ShivinderK/Capstone_Project/HTML coding/HTML Coding.pdf

# IoT Based Garage Door

# Opener: HTML Coding for Web Page

### Dawinder Kaur

(C0765505)

### Group 4

## Content:

- Introduction of ESP32 Wifi Module
- Features of ESP32
- Pinout of ESP32
- Introduction to HTML Coding
- Versions of HTML
- Example of HTML Document
- What is HTML element
- HTML Page Structure
- Introduction of CSS3
- Features of CSS3
- CSS3 Example
- Advantages of CSS3
- References

## Introduction of ESP32 Wifi Module

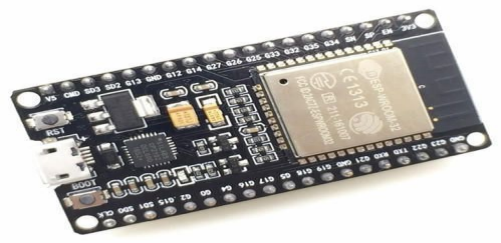
[picture p140: figure]

- ESP32 is a series of low-cost,
low-power system on a chip (https://en.wikipedia.org/wiki/System_on_a_chip)
microcontrollers (https://en.wikipedia.org/wiki/Microcontroller) with integrated Wi-Fi (https://en.wikipedia.org/wiki/Wi-Fi) and dual-mode Bluetooth. (https://en.wikipedia.org/wiki/Bluetooth)
- ESP32 is created and developed by Espressif Systems, a
Shanghai-based Chinese
company, and is manufactured by TSMC using their 40 nm
process.
- It is a successor to the ESP8266 microcontroller.

## Features of ESP32 Wifi module

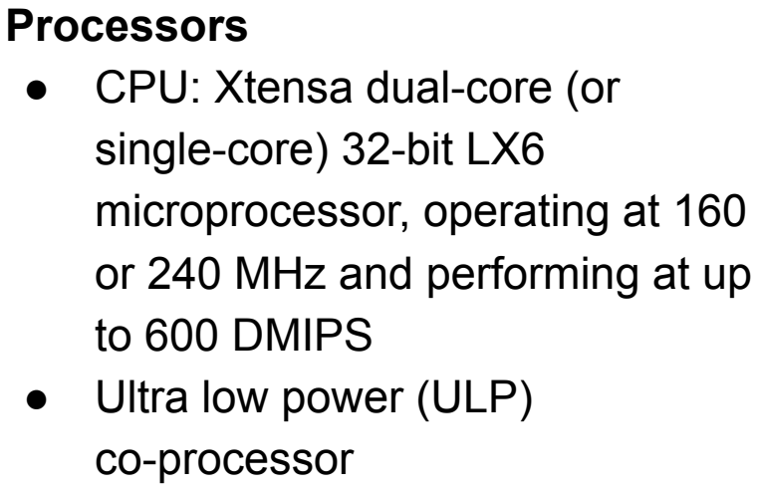
[picture p141: figure]
Processors ● CPU: Xtensa dual-core (or single-core) 32-bit LX6 microprocessor, operating at 160 or 240 MHz and performing at up to 600 DMIPS ● Ultra low power (ULP) co-processor

Peripheral interfaces
- 12-bit SAR ADC (https://en.wikipedia.org/wiki/Successive_approximation_ADC) up to 18
channels
- 2 × 8-bit DACs
- 10 × touch sensors
- 4 × SPI
- 2 × I²S and 2 x I²C interfaces
- 3 × UART
- MMC/eMMC host controller
- SDIO/SPI slave controller

## Features of ESP32 Wifi module

- Ethernet MAC interface with dedicated DMA and IEEE 1588 Precision Time Protocol support
- CAN bus 2.0
- Infrared remote controller (TX/RX, up to 8 channels)
- Motor PWM
- LED PWM (up to 16 channels)
- Hall effect sensor
- Ultra low power analog preamplifier

## Pin Diagram of ESP32 Wifi module

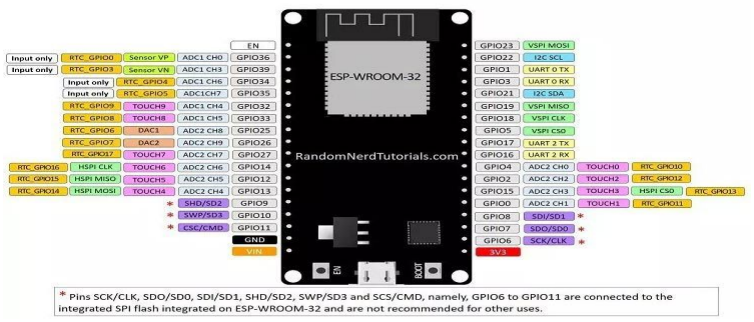
[picture p142: figure]

## Introduction to HTML Coding

HTML is the standard markup language for creating Web pages.

- HTML stands for Hyper Text Markup Language.
- It is a language that we use to create Web pages.
- It describes the structure of Web pages.
- It consists of a series of elements.
- HTML elements tell the browser how to display the content.
- HTML elements label pieces of content such as “this is a heading”, “this is a paragraph”, “this is a link”, etc.

## Introduction to HTML Coding

HTML Version:

- HTML 1.0
- HTML 2
- HTML 3.2
- HTML 4.01
- HTML 5

## Introduction to HTML Coding

HTML 5 is the latest version of HTML language. It was started to use in 2014 and it came up with lots of HTML tags support. It provided support for new form elements like input elements of different types, geolocations, support tags, etc.

The new tags that has been added are Email, password, audio tag, semantic tags and section tag.

## Introduction to HTML Coding

<!DOCTYPE html> | //this declares that this is an HTML5 document
<html> | //this is the root element of HTML page
<head> | //this contains meta information about HTML page
<title>Page Title</title> | //this element is shown in the browser’s title
</head>
<body> | //element defines the document’s body and is the

container for all visible contents like headings,

paragraphs, images, hyperlinks, etc

<h1>My First Heading</h1> | //defines a large heading
<p>My first paragraph.</p> | //defines a paragraph

</body>
</html>

## Introduction to HTML Coding

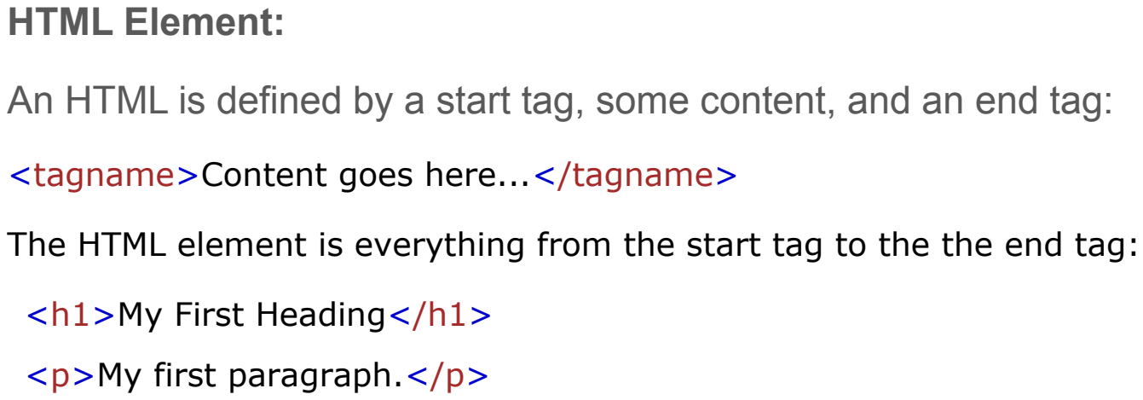
[picture p143: figure]
HTML Element:; <tagname>Content goes here...</tagname>; <h1>My First Heading</h1>; <p>My first paragraph.</p>

An HTML is defined by a start tag, some content, and an end tag:

The HTML element is everything from the start tag to the the end tag:

## Introduction to HTML Coding

Start Tag | Element Content | End Tag
<h1> | My First Heading | </h1>
<p> | My first paragraph | </p>
<br> | none | none

## Introduction to HTML Coding

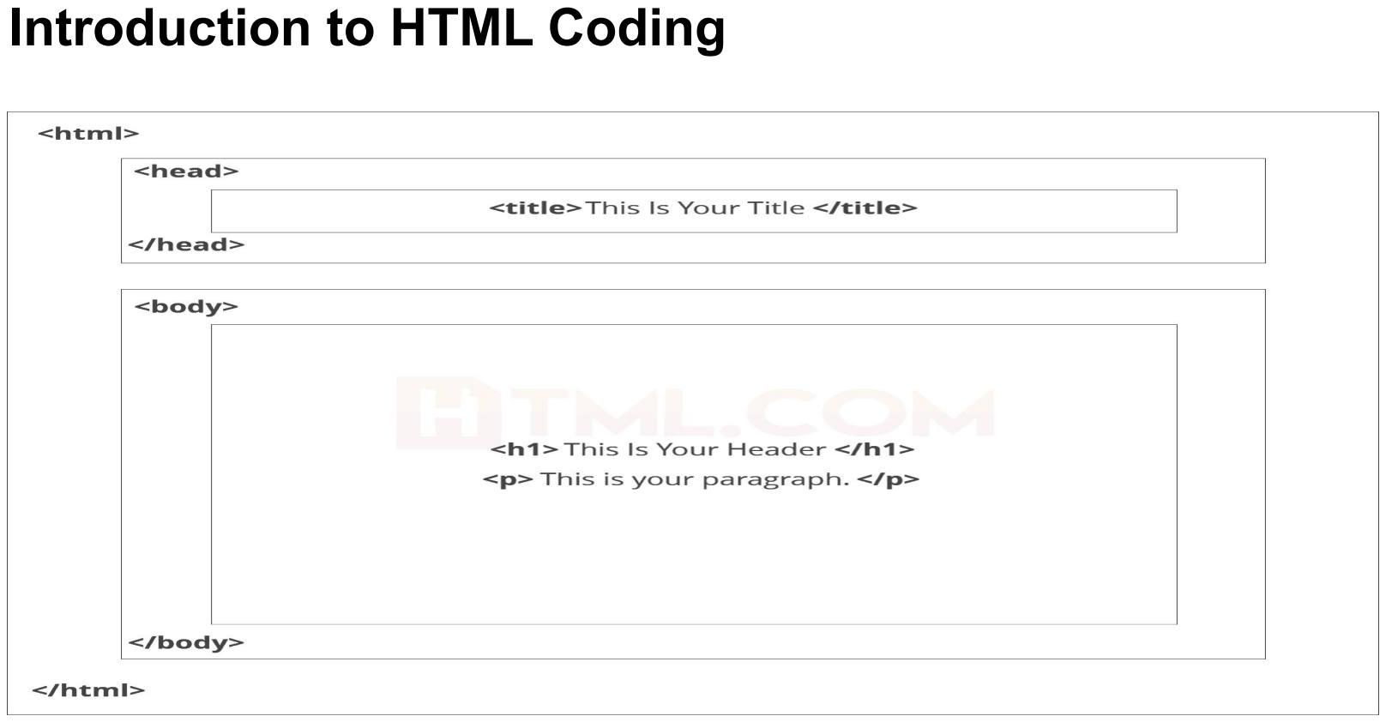
[picture p144: page 13]

## Introduction CSS3(Cascading Style Sheets):

Cascading Style Sheets (CSS) is a language that is used to illustrate the look, style, and format of a document written in any markup language.

In simple words, it is used to style and organize the layout of Web pages.

CSS3 is the latest version of an earlier CSS version, CSS2.

A significant change in CSS3 in comparison to CSS2 is the introduction of modules.

The benefit of this functionality is that it allows the specification to be finalized and accept faster, as segments are finalized and accepted in portions.

## Introduction CSS3(Cascading Style Sheets):

Some of the key modules of CSS3 are:

- Box model
- Image values and replaced content
- Text effects
- Selectors
- Backgrounds and borders
- Animations
- User interface (UI)
- Multiple column layouts
- 2D/3D transformations.

## Introduction CSS3(Cascading Style Sheets):

body | {
background-color: | lightblue;
}
h1 | { | //<h1> This is a heading
color: | white;
text-align: | center;
}
p | { | //<p> This is a paragraph
font-family: | verdana;
font-size: | 20px;
}

## Introduction CSS3(Cascading Style Sheets):

Advantages of CSS3

- CSS3 provides a consistent and precise positioning of navigable elements.
- It is easy to customize a web page as it can be done by merely altering a modular file.
- Graphics are easier in CSS3, thus making it easy to make the site appealing.
- It permits online videos to be seen without using third-party plug-ins.
- CSS3 is economical, time-saving, and most browsers support it.

## HTML Coding on Notepad:

HTML Programming on Notepad:

1. Open Notepad
2. Write HTML/CSS3 code
3. Save the file named as web.html (with .html extension so that it can run on browser).
4. Go to the location where u saved the file.
5. Click on file and choose open with chrome browser
6. Web page will appear on web browser.

## HTML Coding on Notepad:

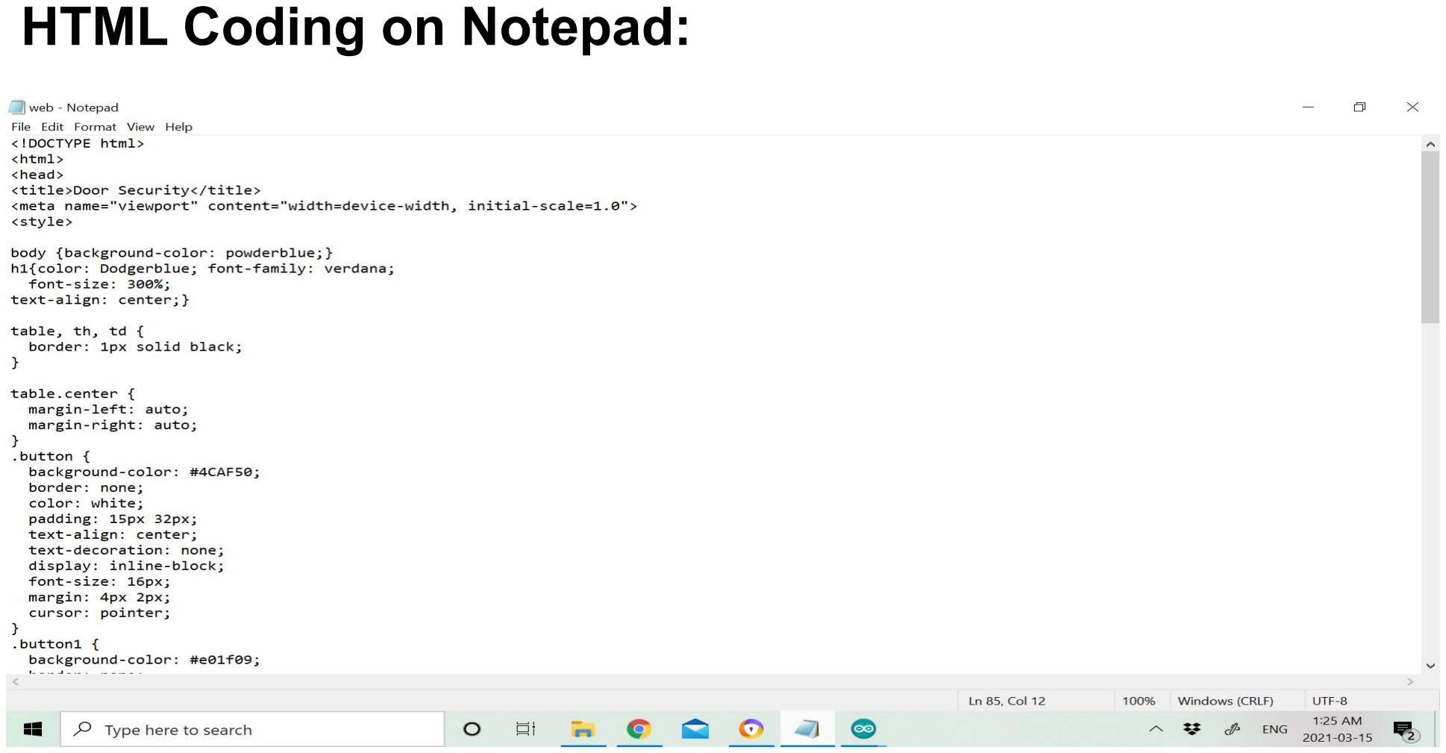
[picture p145: page 19]

## HTML Coding on Notepad:

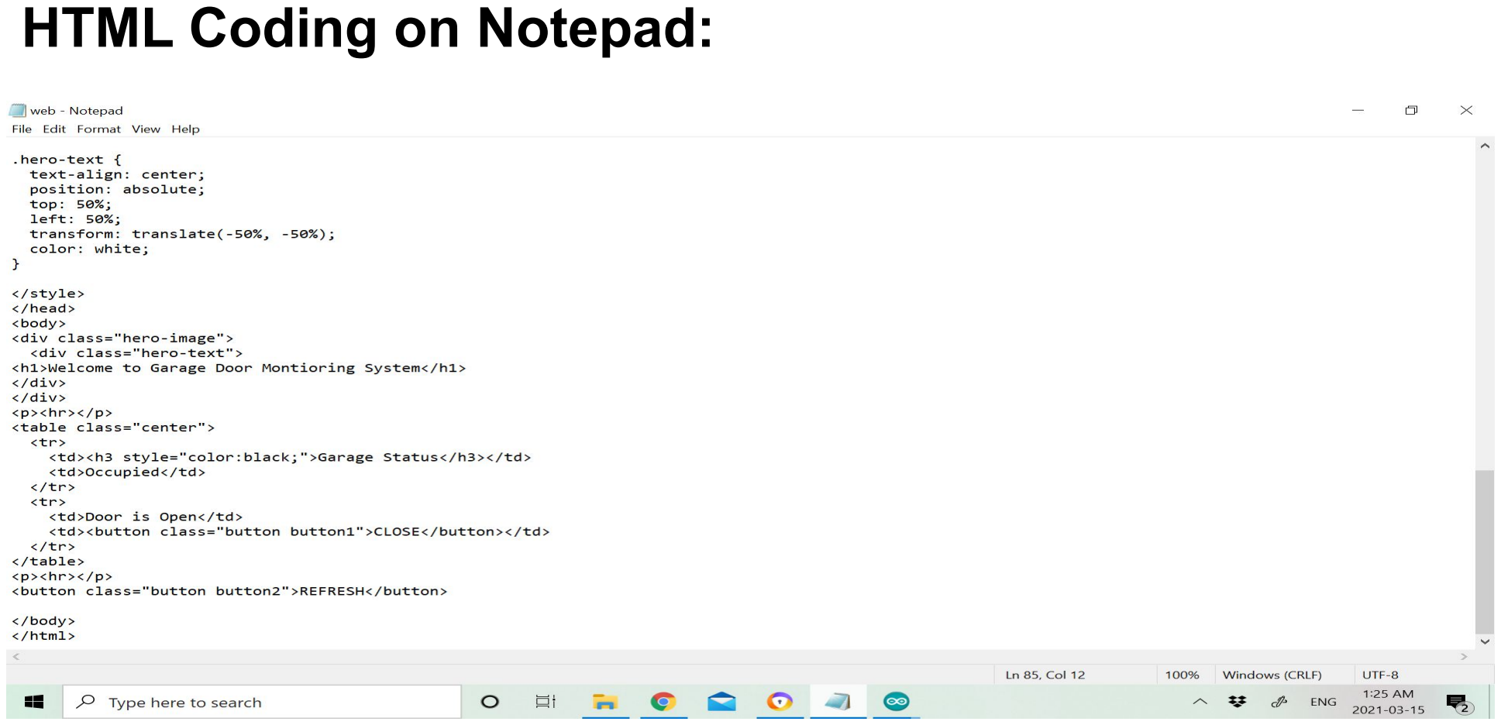
[picture p146: page 20]

## HTML Coding on Notepad: Output

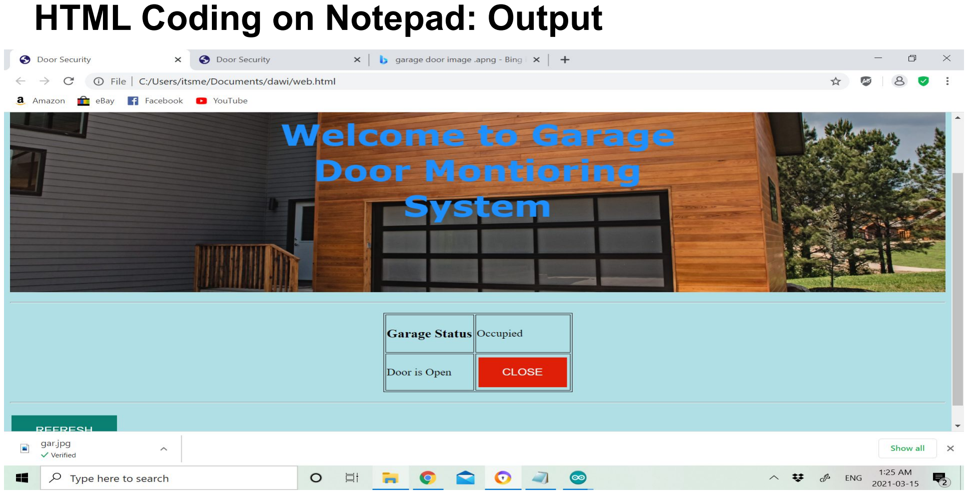
[picture p147: page 21]

## HTML coding on ESP32:

HTML coding on ESP32:

- Open arduino ide
- Write arduino ide code for esp32 wifi connectivity and in void loop{ } area add the html code using command “client.print {html code here}”
- Save the file
- Compile it and execute it by connecting ESP32 with system.
- Output will appear in serial monitor

## HTML coding on ESP32:

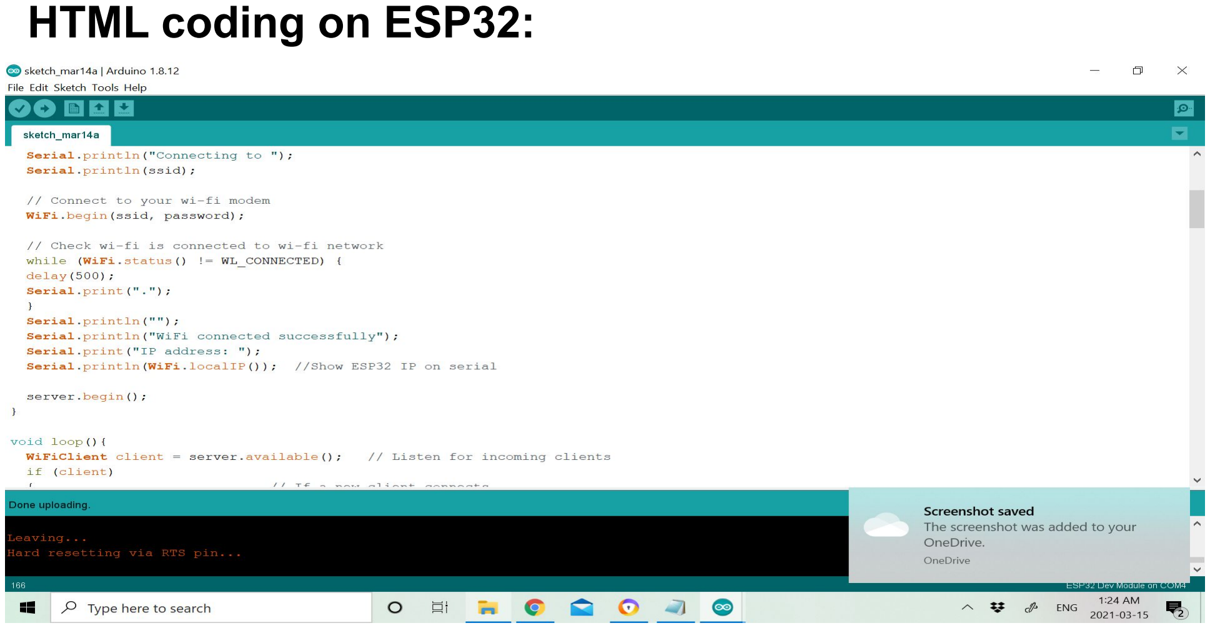
[picture p148: page 23]

## HTML coding on ESP32:

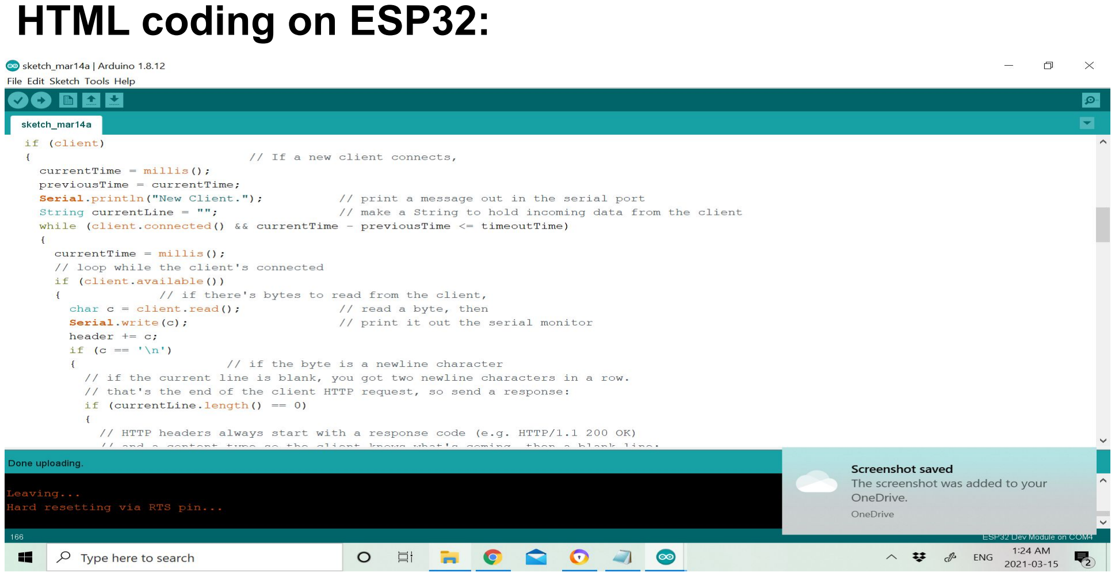
[picture p149: page 24]

## HTML coding on ESP32:

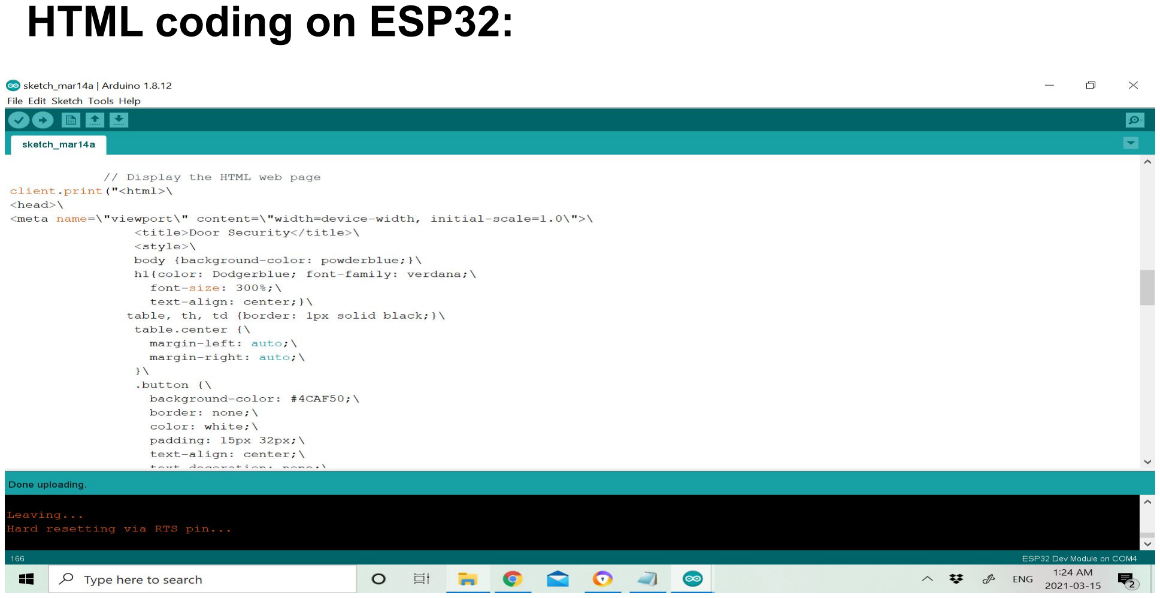
[picture p150: page 25]

## HTML coding on ESP32:

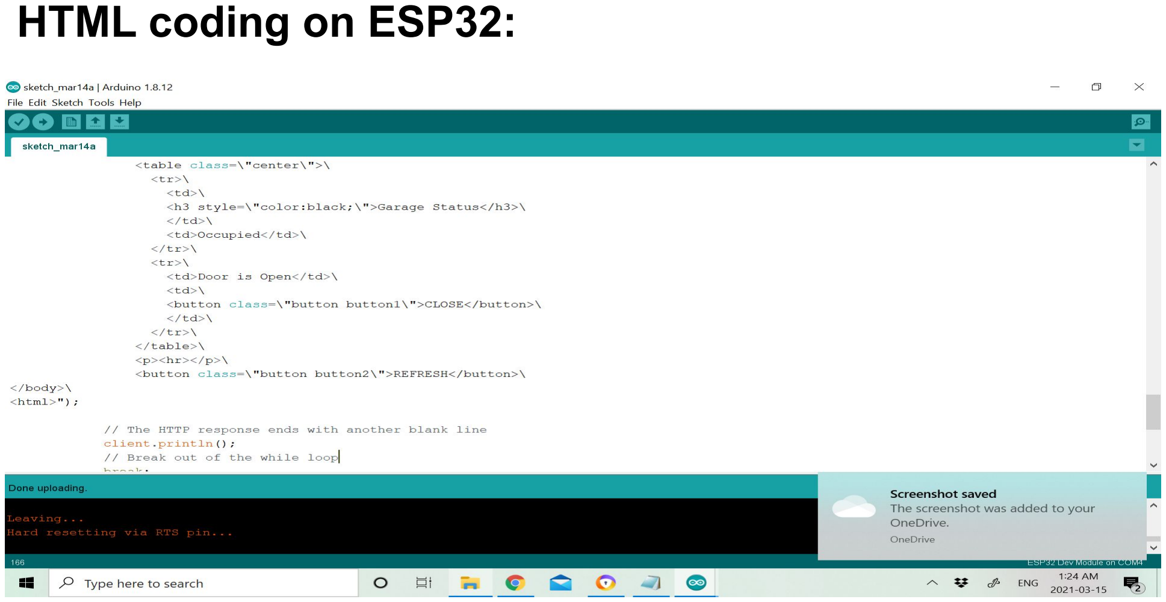
[picture p151: page 26]

## HTML coding on ESP32:

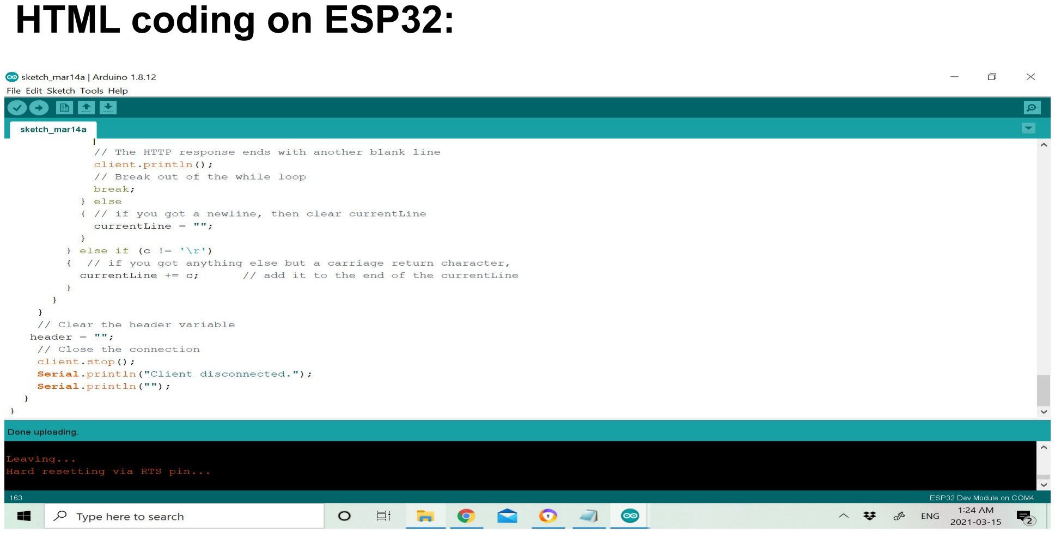
[picture p152: page 27]

## HTML coding on ESP32: Output

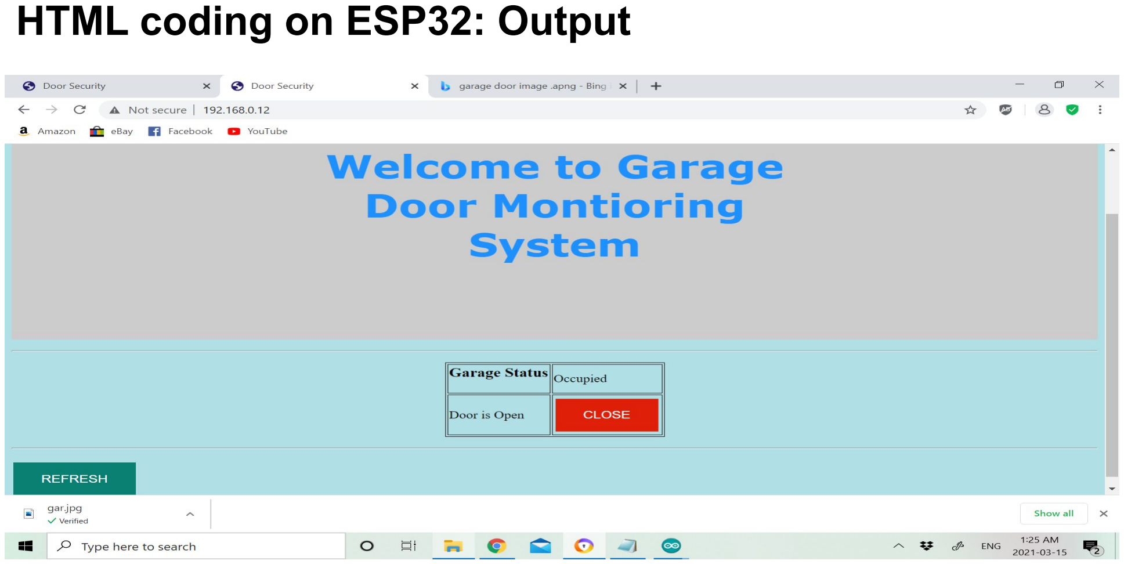
[picture p153: page 28]

## References:

- Features of ESP32 retrieved from Esp32.net; features and specifications URL: http://esp32.net/
- Image of block diagram retrieved from Esp32.net; features and specifications URL: http://esp32.net/
- CSS3 retrieved from eduba.co;what is CSS3? URL: https://www.educba.com/what-is-css3/
- HTML retrieved from w3schools.com; URL: https://www.w3schools.com/html/default.asp
- ESP32 coding retrieved from randomnerdtutorial.com; URL: https://randomnerdtutorials.com/esp32-web-server-arduino-ide/
