ShivinderK/Capstone_Project/Interfacing BBB with PushButton/IMG-4762.jpg

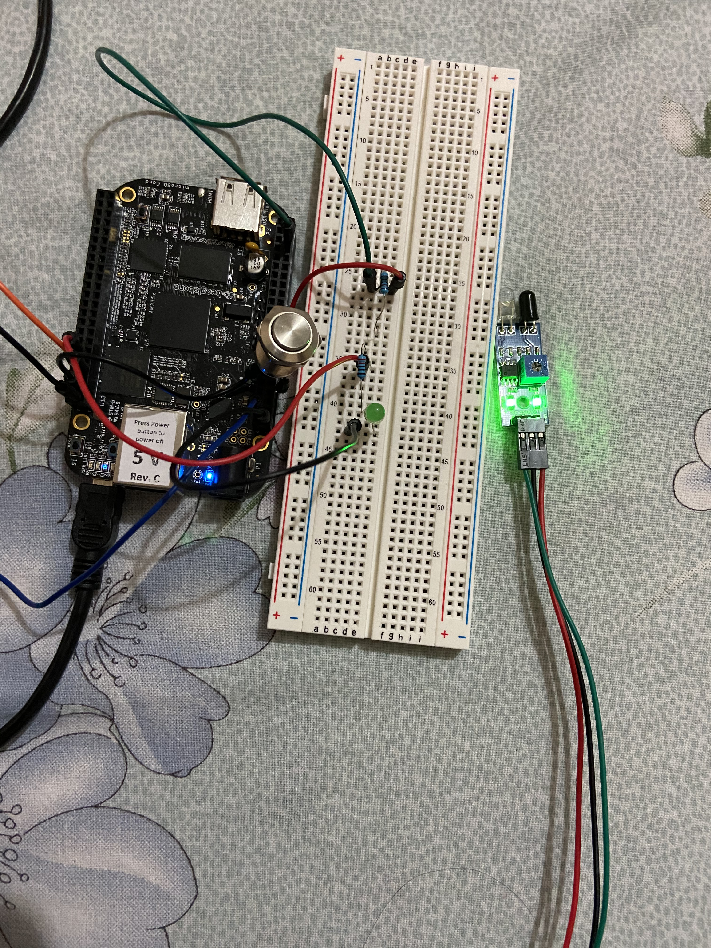
Interfacing BBB with PushButton/IMG-4762.jpg
