ShivinderK/Capstone_Project/interfacing PIR sensor 1/IMG-0326.jpg

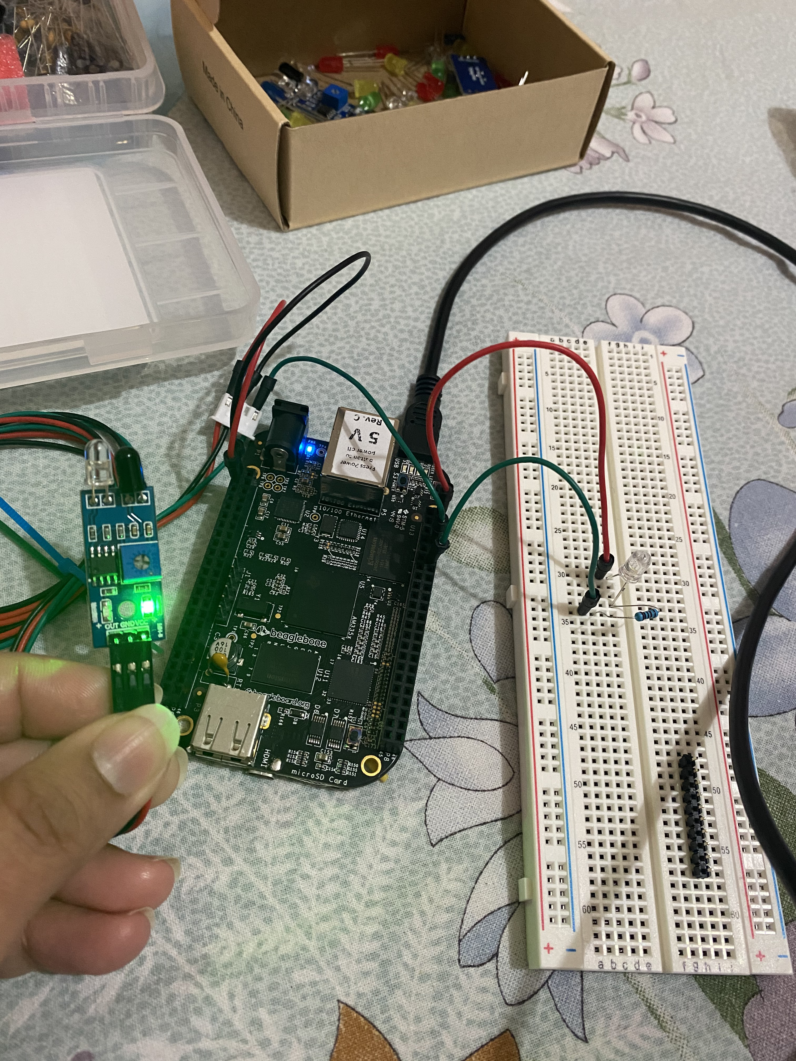
interfacing PIR sensor 1/IMG-0326.jpg
