ShivinderK/Capstone_Project/interfacing PIR sensor 1/IMG-0327.jpg

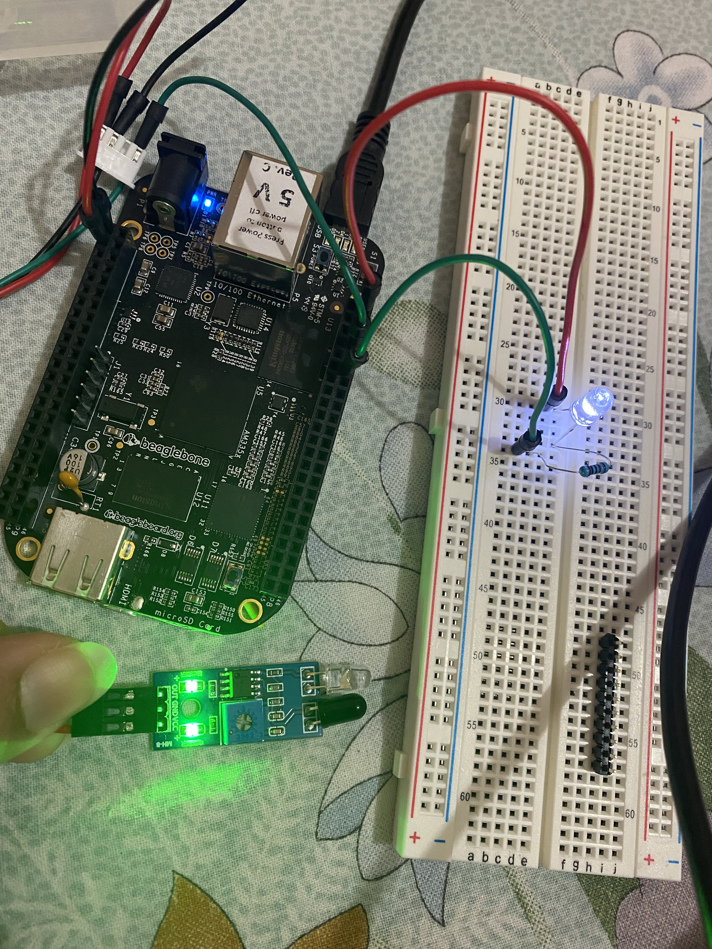
interfacing PIR sensor 1/IMG-0327.jpg
